reivaxy/iotinator/resources/4_modules.jpg

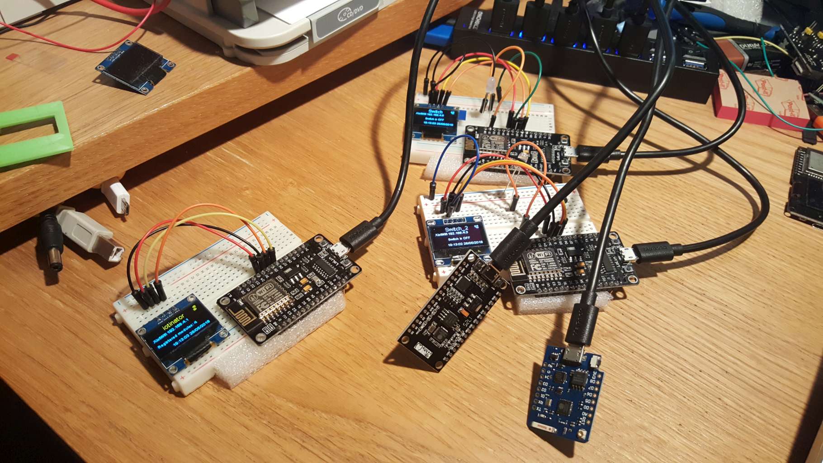
resources/4_modules.jpg
