reivaxy/iotinator/resources/boards.jpg

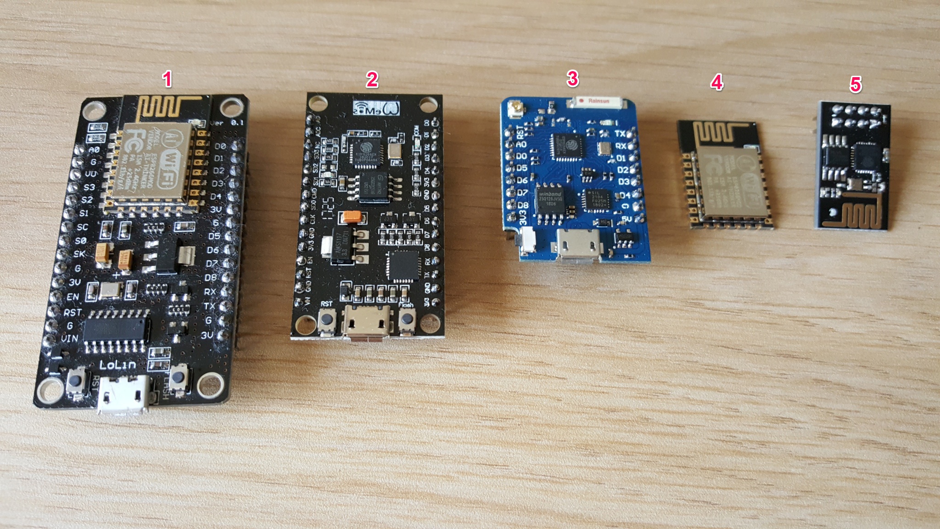
resources/boards.jpg
