reivaxy/iotinator/resources/customESP01.jpg

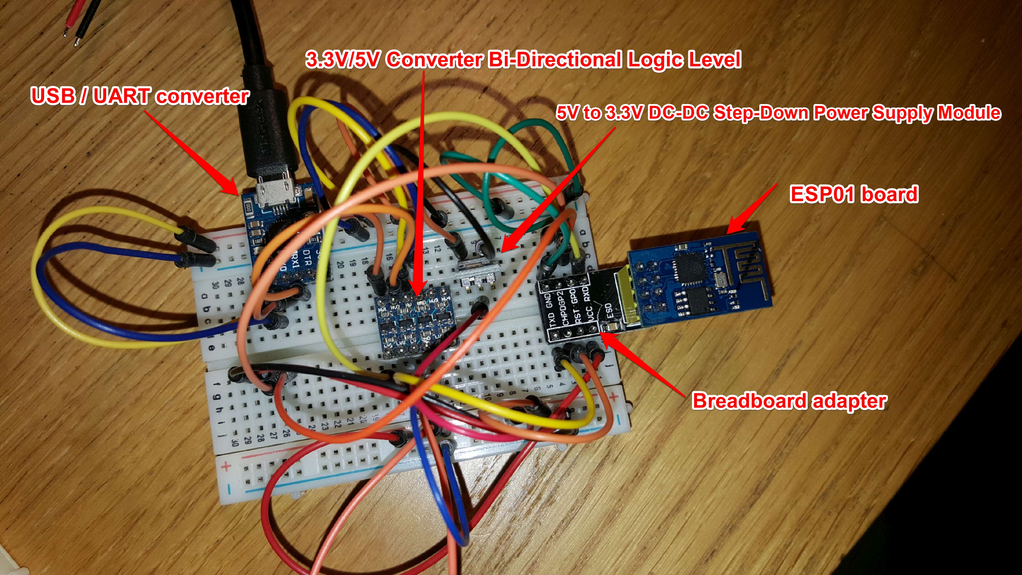
resources/customESP01.jpg
