reivaxy/iotinator/resources/esp01.jpg

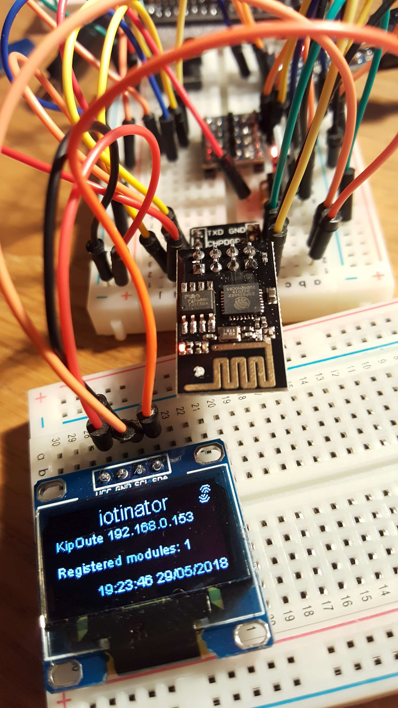
resources/esp01.jpg
