reivaxy/iotinator/resources/esp32.jpg

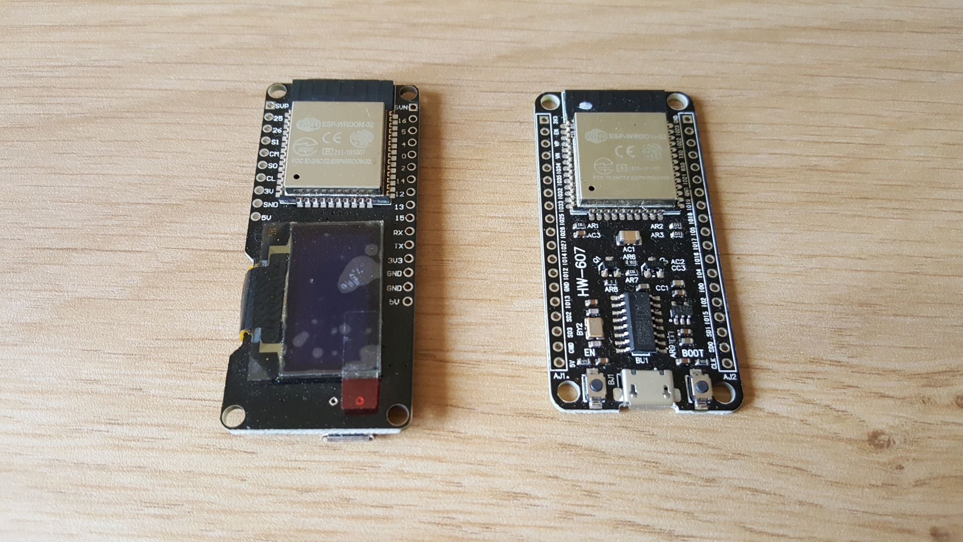
resources/esp32.jpg
