reivaxy/iotinator/resources/glyphEditor.png

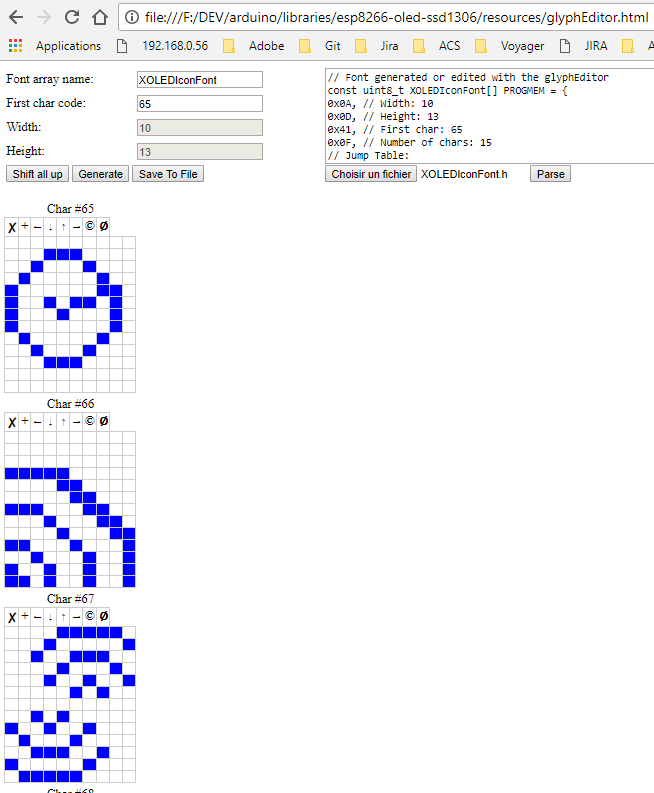
resources/glyphEditor.png
