reivaxy/iotinator/resources/heap.png

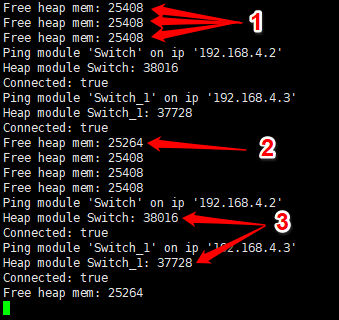
resources/heap.png
