reivaxy/iotinator/resources/iotinator_init_done.jpg

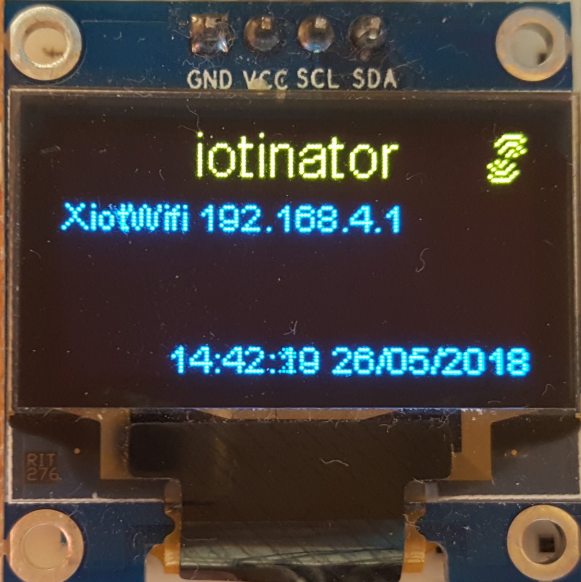
resources/iotinator_init_done.jpg
