reivaxy/iotinator/resources/iotinator_registration.jpg

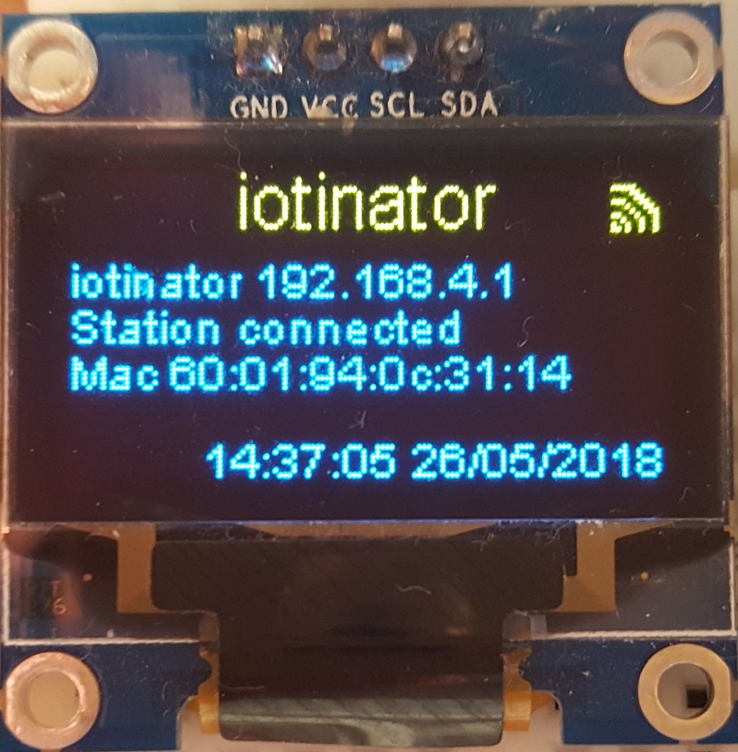
resources/iotinator_registration.jpg
