reivaxy/iotinator/resources/iotinator_waiting.jpg

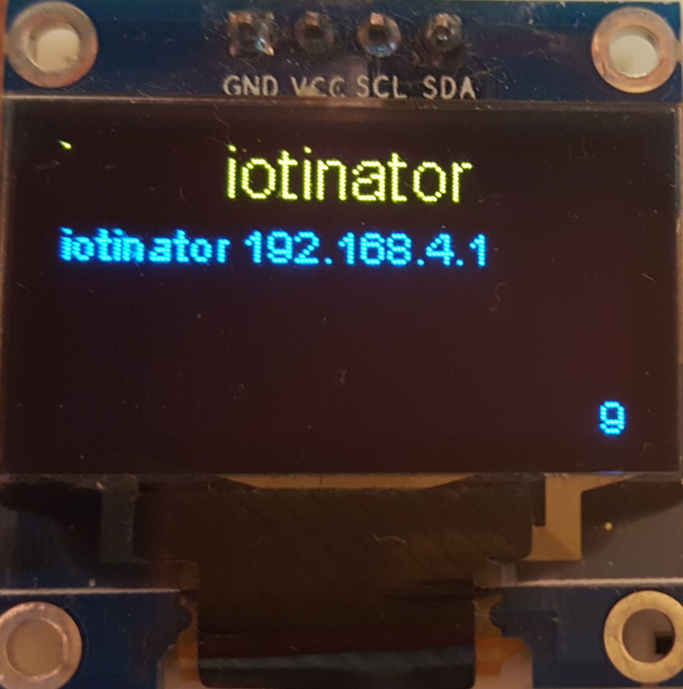
resources/iotinator_waiting.jpg
