reivaxy/iotinator/resources/OTA/OTA_loading.jpg

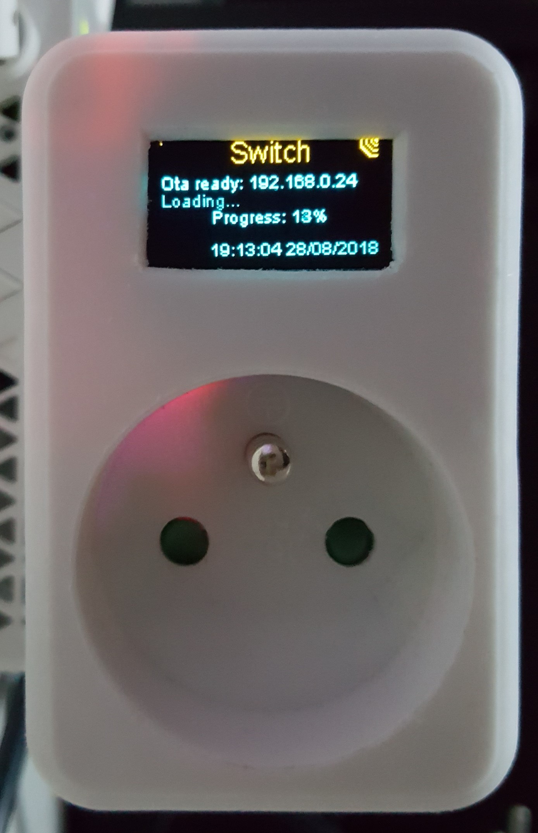
resources/OTA/OTA_loading.jpg
