reivaxy/iotinator/resources/OTA/OTA_ready.jpg

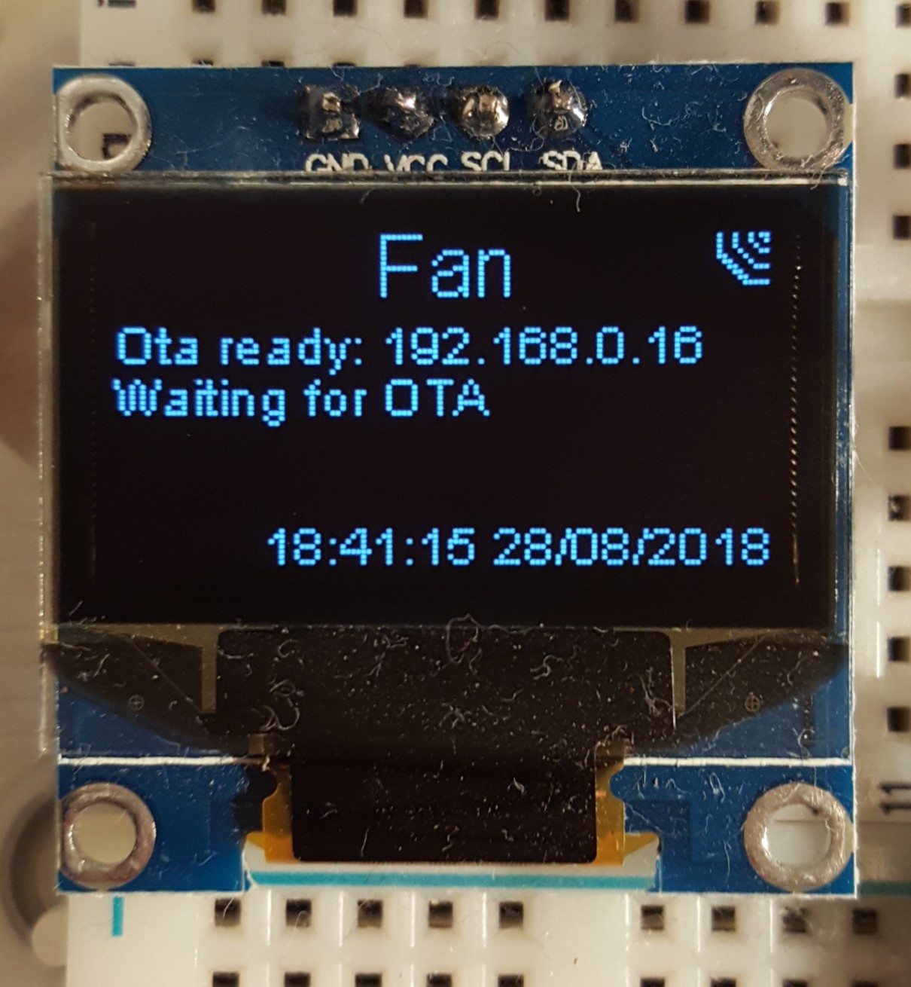
resources/OTA/OTA_ready.jpg
