reivaxy/iotinator/resources/prototype/backOpen.jpg

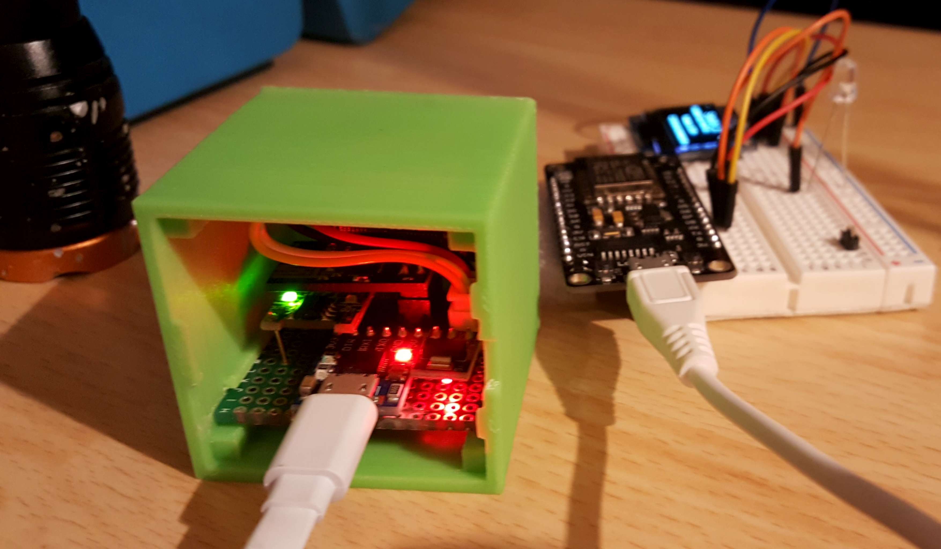
resources/prototype/backOpen.jpg
