reivaxy/iotinator/resources/prototype/backView.jpg

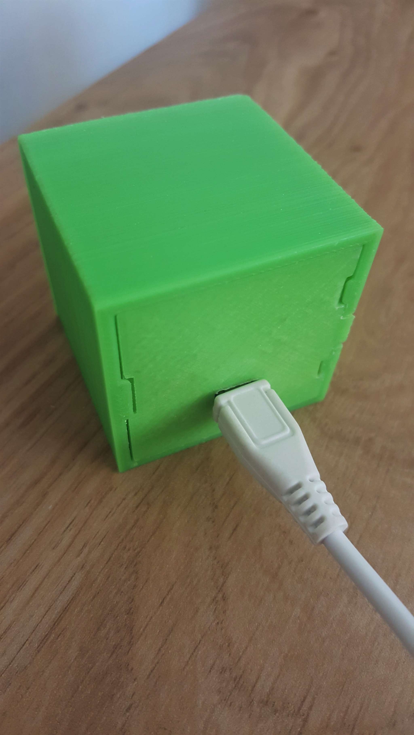
resources/prototype/backView.jpg
