reivaxy/iotinator/resources/prototype/case.jpg

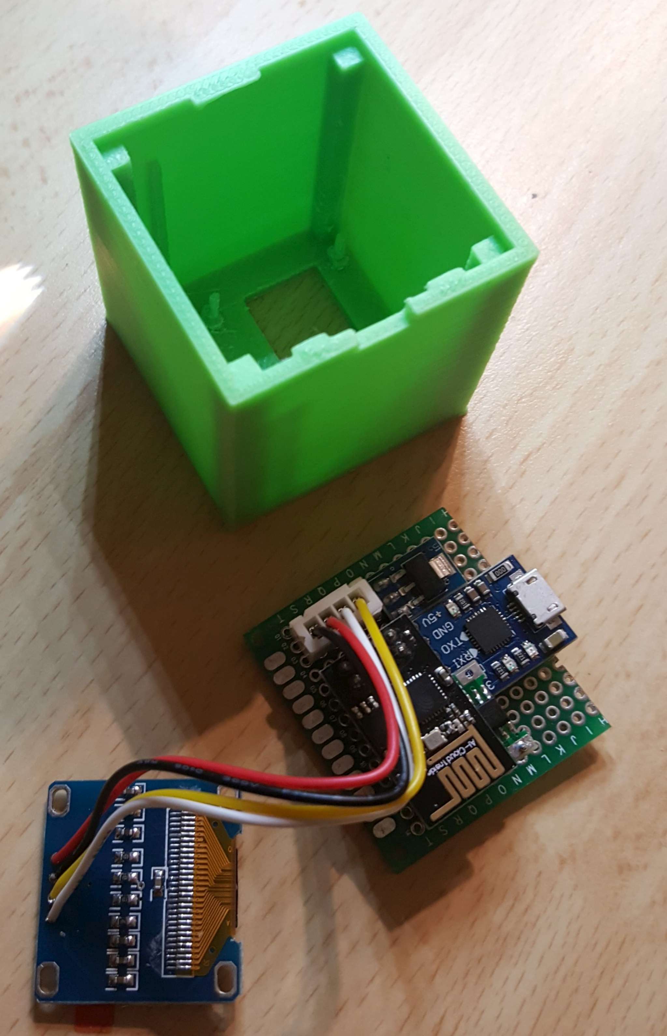
resources/prototype/case.jpg
