reivaxy/iotinator/resources/prototype/inPlace.jpg

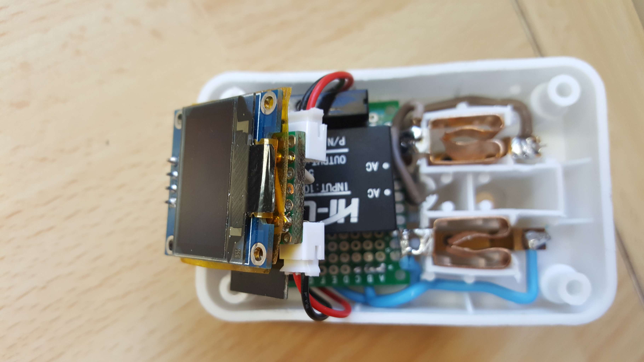
resources/prototype/inPlace.jpg
