reivaxy/iotinator/resources/prototype/mounted.jpg

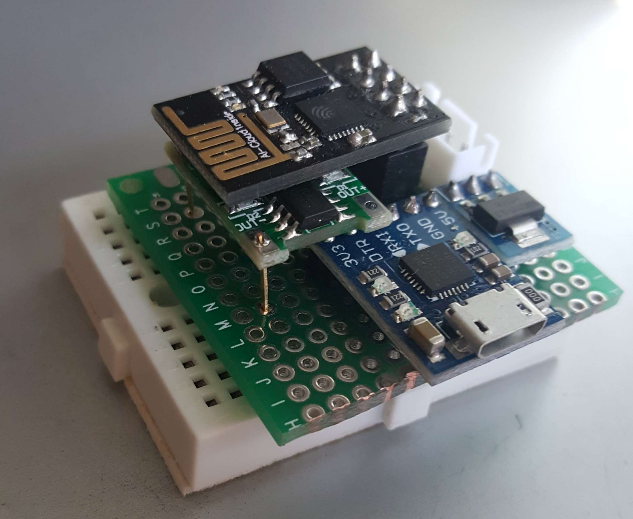
resources/prototype/mounted.jpg
