reivaxy/iotinator/resources/prototype/positioning.jpg

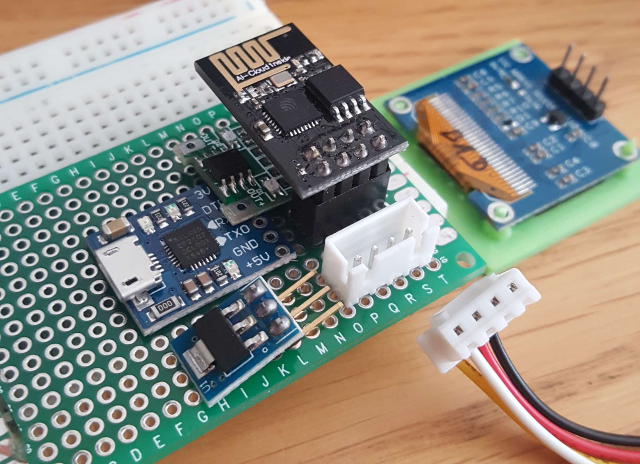
resources/prototype/positioning.jpg
