reivaxy/iotinator/resources/prototype/powerDown.jpg

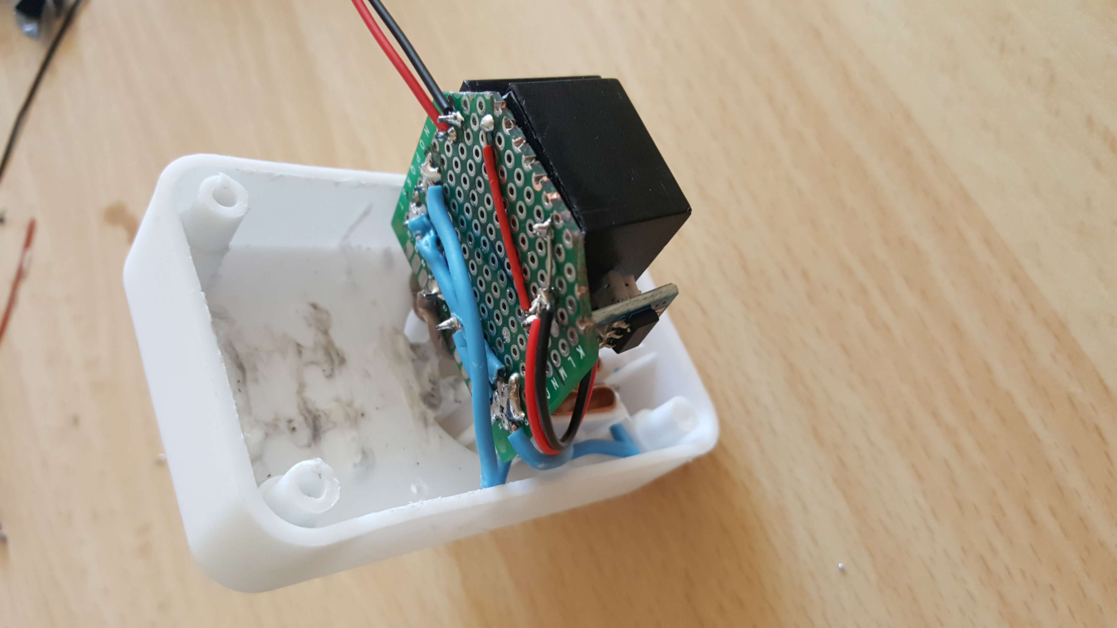
resources/prototype/powerDown.jpg
