reivaxy/iotinator/resources/prototype/powerSocketNew.jpg

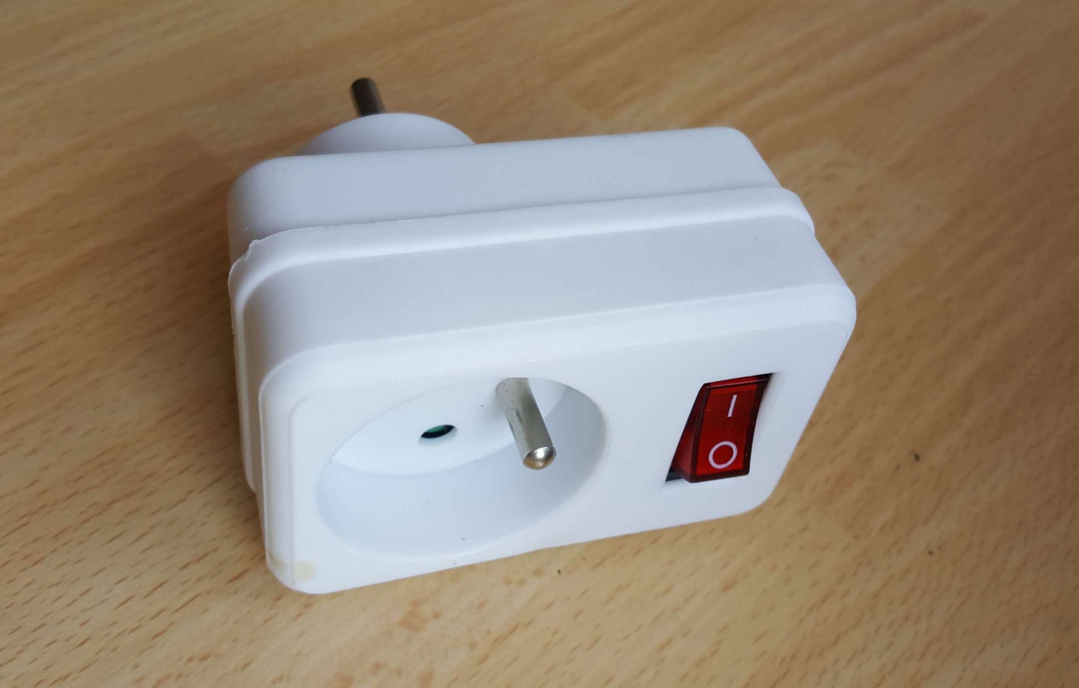
resources/prototype/powerSocketNew.jpg
