reivaxy/iotinator/resources/prototype/powerSocketOpen.jpg

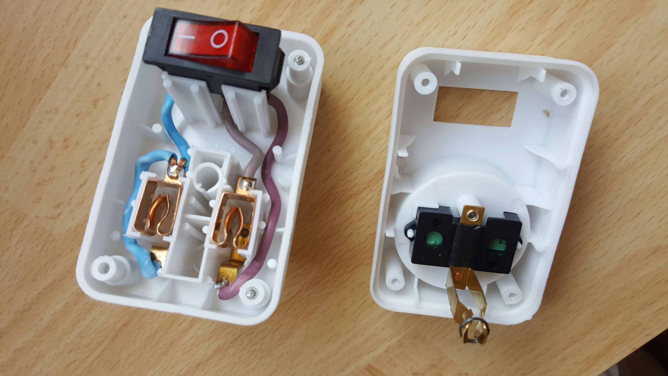
resources/prototype/powerSocketOpen.jpg
