reivaxy/iotinator/resources/prototype/ready.jpg

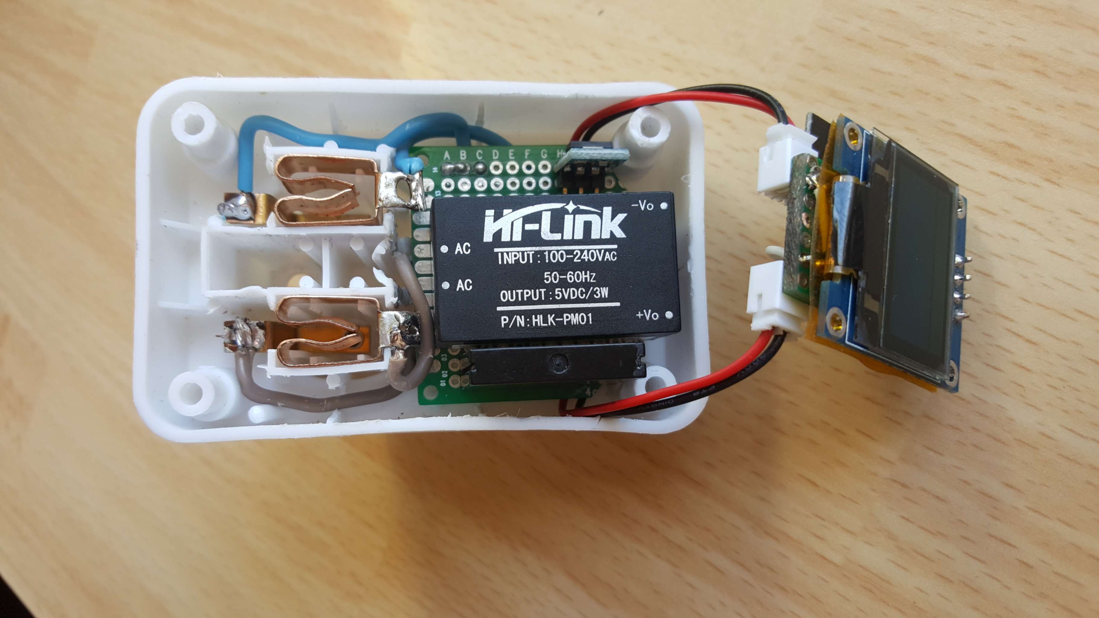
resources/prototype/ready.jpg
