reivaxy/iotinator/resources/prototype/sandwitch.jpg

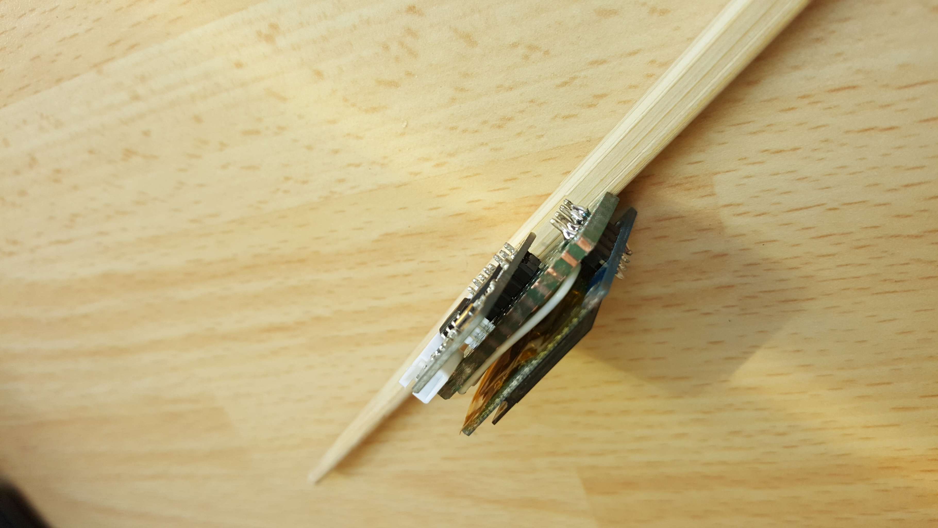
resources/prototype/sandwitch.jpg
