reivaxy/iotinator/resources/prototype/withScreen.jpg

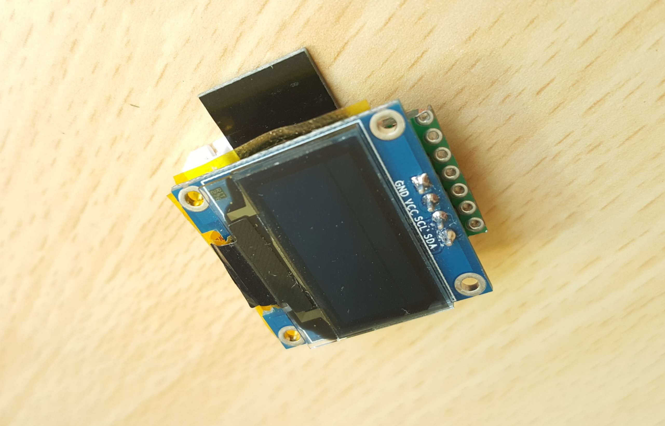
resources/prototype/withScreen.jpg
