reivaxy/iotinator/resources/switch_init1.jpg

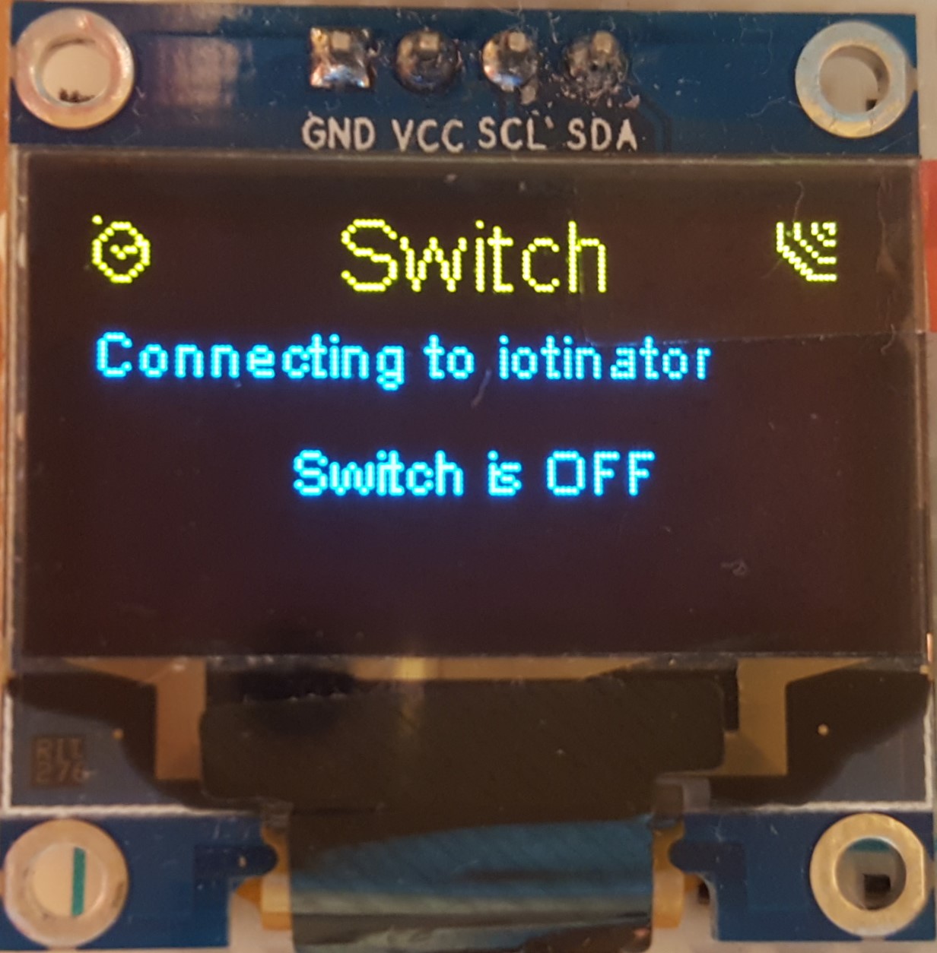
resources/switch_init1.jpg
