reivaxy/iotinator/resources/switch_init2.jpg

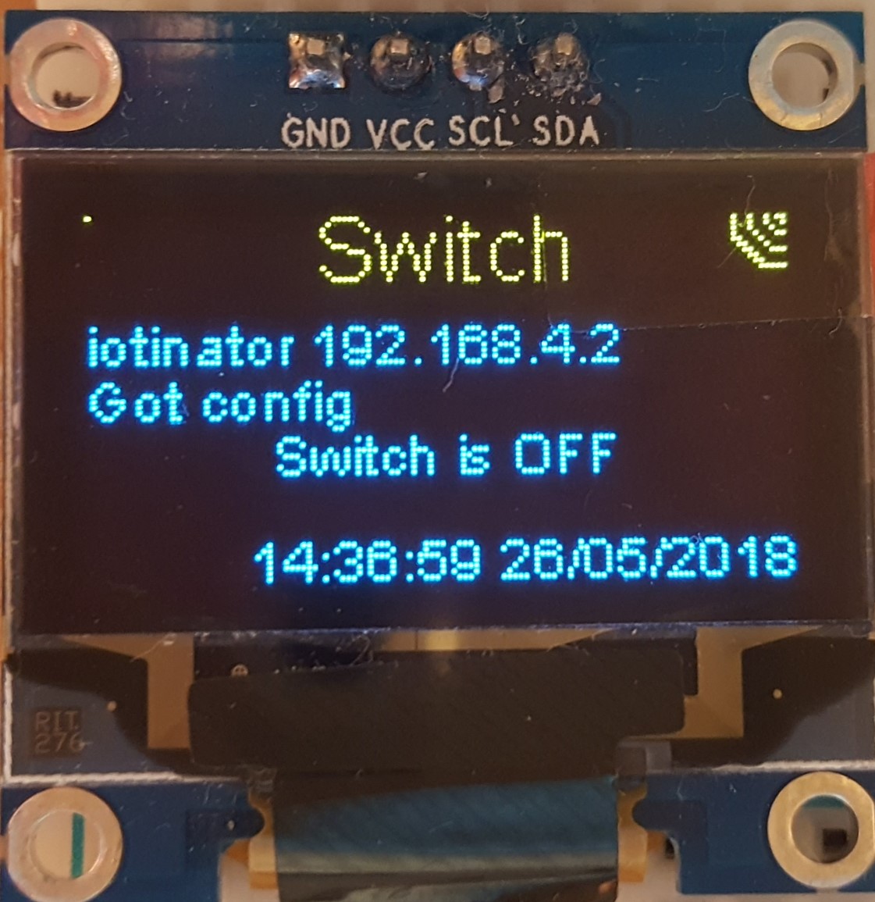
resources/switch_init2.jpg
