reivaxy/iotinator/resources/switch_on.jpg

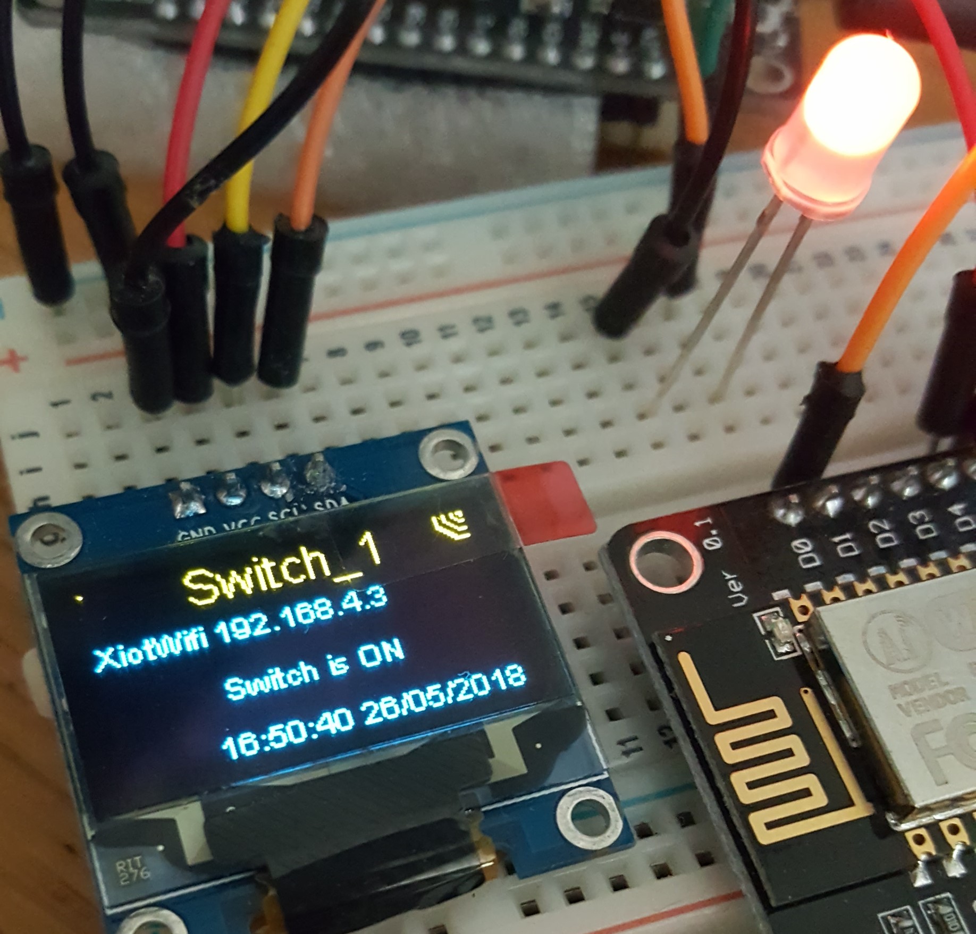
resources/switch_on.jpg
