reivaxy/iotinator/resources/usbESP01.jpg

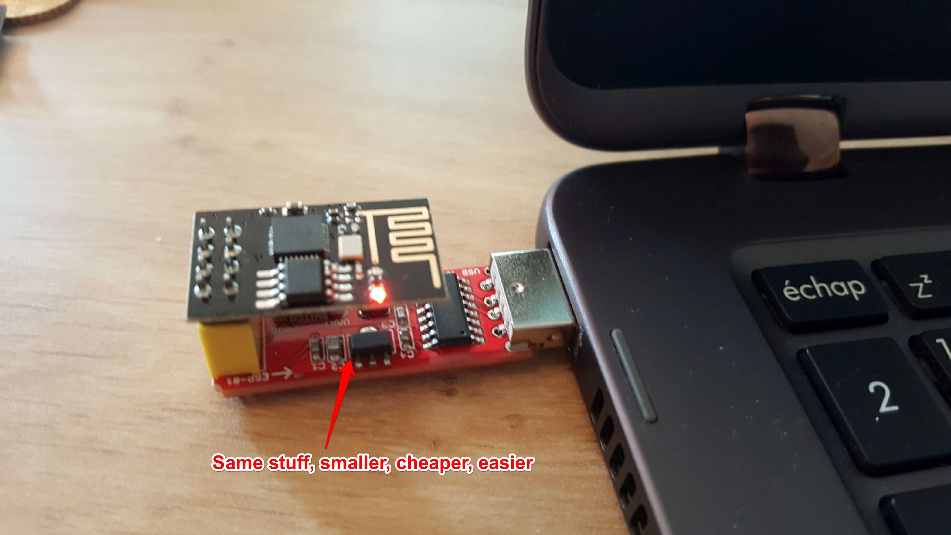
resources/usbESP01.jpg
