reivaxy/iotinator/resources/vcc_gnd.jpg

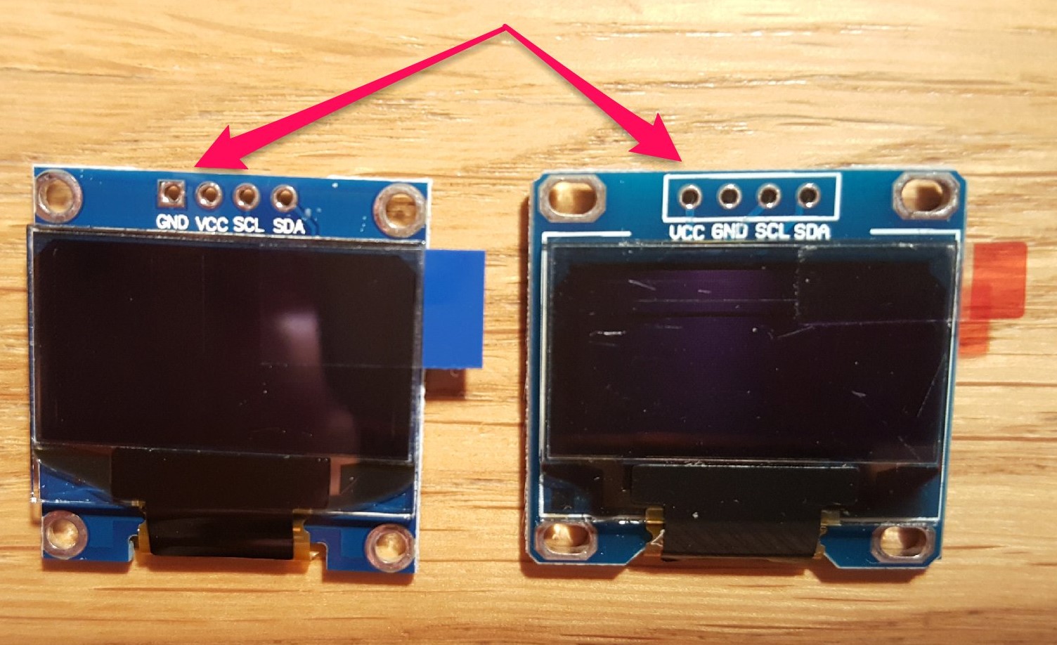
resources/vcc_gnd.jpg
