reivaxy/iotinator/resources/webApp_init.png

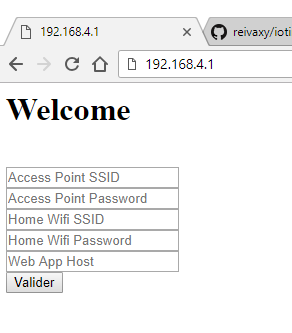
resources/webApp_init.png
