reivaxy/iotinator/resources/prototype/switchComponents.jpg

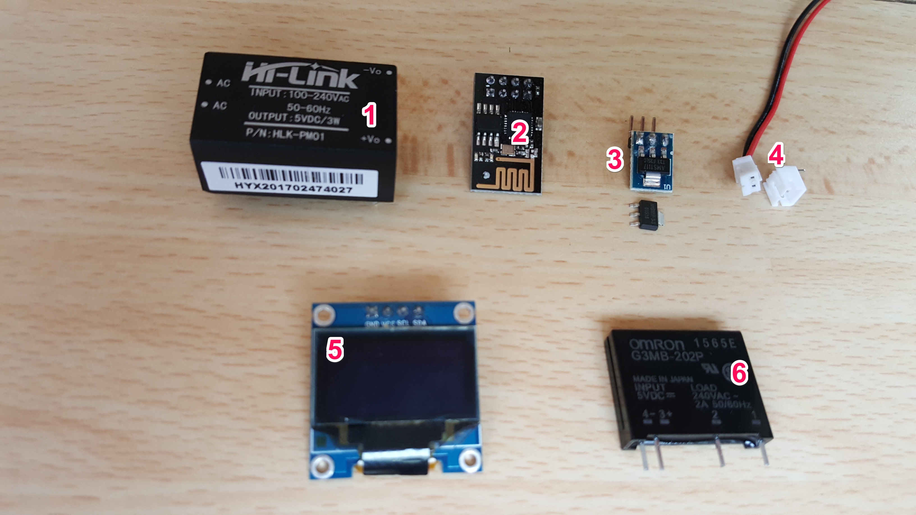
resources/prototype/switchComponents.jpg
