reivaxy/iotinator/resources/crappy_print.jpg

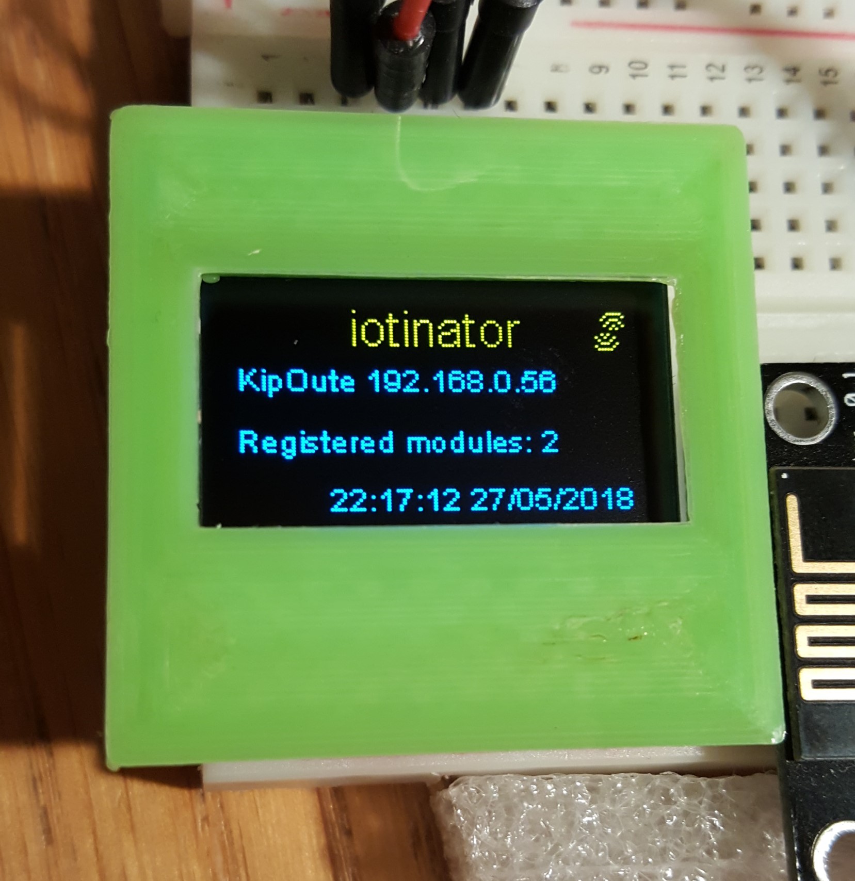
resources/crappy_print.jpg
