reivaxy/iotinator/resources/printed_panel.jpg

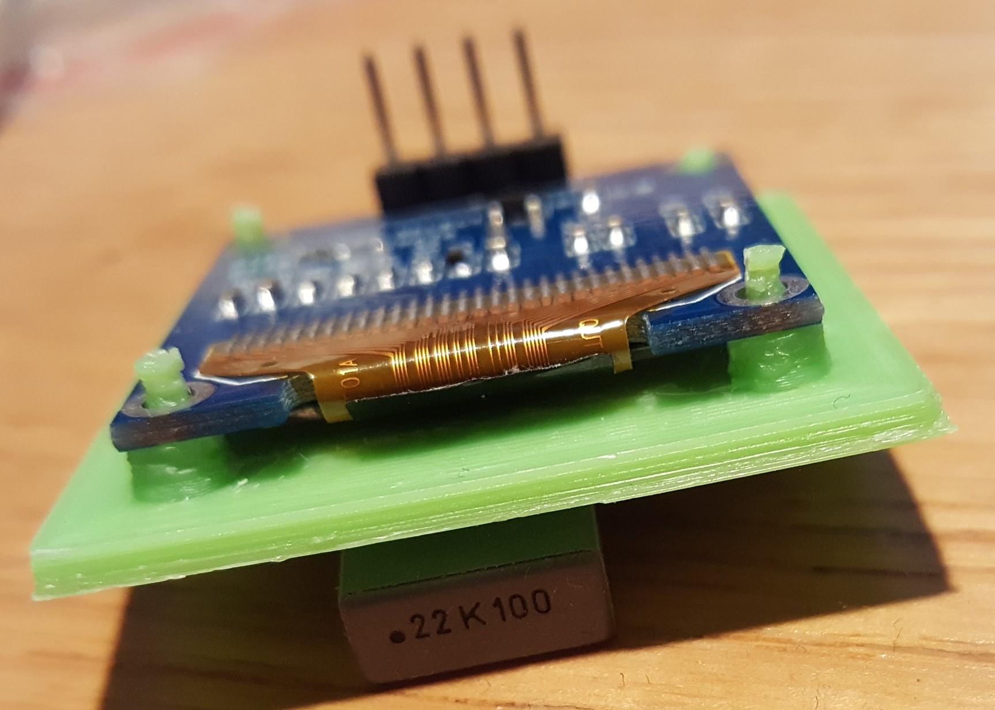
resources/printed_panel.jpg
