reivaxy/iotinator/resources/prototype/esp01Wiring.jpg

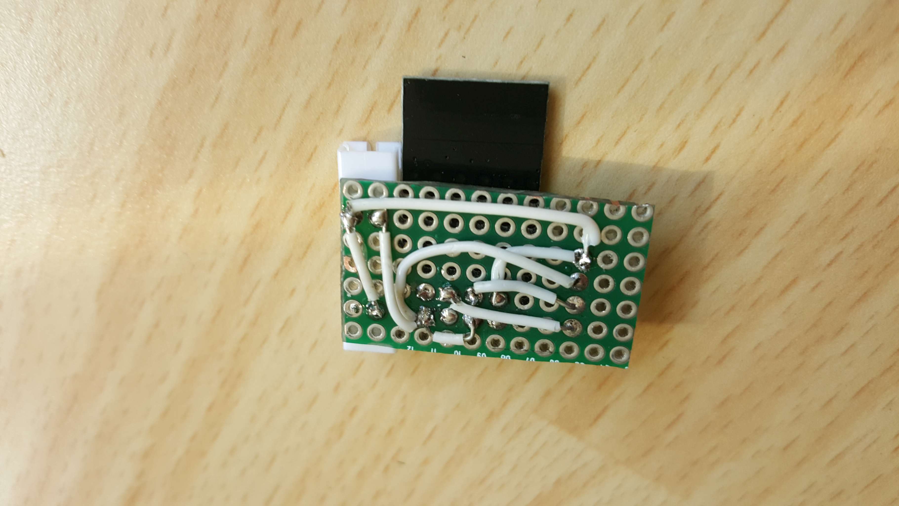
resources/prototype/esp01Wiring.jpg
