reivaxy/iotinator/resources/prototype/test.jpg

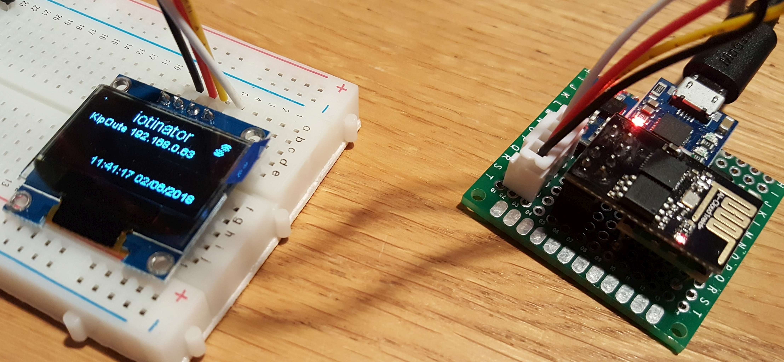
resources/prototype/test.jpg
