reivaxy/iotinator/resources/prototype/testingDCPower.jpg

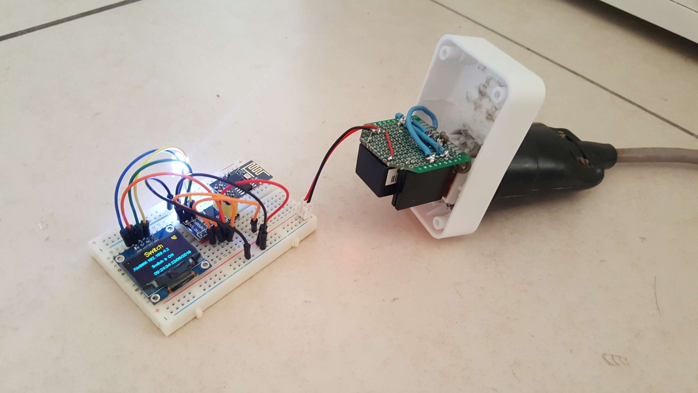
resources/prototype/testingDCPower.jpg
