reivaxy/iotinator/resources/webApp_debug.png

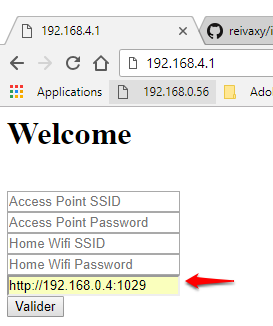
resources/webApp_debug.png
