reivaxy/iotinator/iotinator/src/Agent.cpp

/**
 *  Class handling Agent module registered in iotinator master
 *  Xavier Grosjean 2018
 *  Creative Commons Attribution-NonCommercial-ShareAlike 4.0 International Public License
 */

#include "Agent.h"

/*********************************************************************
 * Class to handle one agent module in master
 *
 *********************************************************************/
Agent::Agent(const char* name, const char* mac, XIOTModule* module) {
  XUtils::safeStringCopy(_name, name, NAME_MAX_LENGTH);
  XUtils::safeStringCopy(_mac, mac, NAME_MAX_LENGTH);
  _module = module;
  *_globalStatus = 0;
}

Agent::~Agent() {
  free(_custom);
}

const char* Agent::getName() {
  Debug("Agent::getName\n");
  return _name;
}
void Agent::setName(const char* name) {
  XUtils::safeStringCopy(_name, name, NAME_MAX_LENGTH);
}

const char* Agent::getIP() {
  Debug("Agent::getIP\n");
  return _ip;
}

const char* Agent::getMAC() {
  Debug("Agent::getMAC\n");
  return _mac;
}

void Agent::setIP(const char* ip) {
  XUtils::safeStringCopy(_ip, ip, DOUBLE_IP_MAX_LENGTH);
}

void Agent::setUiClassName(const char* uiClassName) {
  XUtils::safeStringCopy(_uiClassName, uiClassName, UI_CLASS_NAME_MAX_LENGTH);
}
const char* Agent::getUiClassName() {
  return _uiClassName;
}

int8_t Agent::getConnected() {
  return _connected;
}

void Agent::setToRename(bool flag) {
  _toRename = flag;
}

bool Agent::getToRename() {
  return _toRename;
}

void Agent::setHeap(uint32_t heap) {
  _heap = heap;
}

uint32_t Agent::getHeap() {
  return _heap;
}

bool Agent::getCanSleep() {
  return _canSleep;
}

void Agent::setCanSleep(bool canSleep) {
  _canSleep = canSleep;
}

int Agent::getPingPeriod() {
  return _pingPeriod;
}

void Agent::setPingPeriod(int pingPeriod) {
  // If value too small, keep default (legacy: when absent, value is 0)
  if(pingPeriod >= MIN_PING_PERIOD ) {
    _pingPeriod = pingPeriod;
  } else {
    _pingPeriod = 0;
  }
}
time_t Agent::getLastPing() {
  return _lastPing;
}

void Agent::setLastPing(time_t timestamp) {
  _lastPing = timestamp;
}

void Agent::setCustom(const char *custom) {
  Debug("Agent::setCustom\n");
  free(_custom); // This field is manually allocated, so it must be freed.
  _custom = NULL;

  if(custom == NULL) {
    _custom = NULL;
    return;
  }
  int size = strlen(custom);
  if(size > MAX_CUSTOM_DATA_SIZE) {
    Serial.println(CUSTOM_DATA_TOO_BIG_VALUE);
    size = strlen(CUSTOM_DATA_TOO_BIG_VALUE) ;
    _custom = (char *)malloc(size + 1);   // Will need to be freed, when we unregister agent, or overwrite one...
    XUtils::safeStringCopy(_custom, CUSTOM_DATA_TOO_BIG_VALUE, size);
  } else {
    _custom = (char *)malloc(size + 1);   // Will need to be freed, when we unregister agent, or overwrite one...
    XUtils::safeStringCopy(_custom, custom, size);
  }
}

const char* Agent::getCustom() {
  Debug("Agent::getCustom\n");
  if(_custom != NULL) {
    if(strcmp(_custom, CUSTOM_DATA_TOO_BIG_VALUE) == 0) {
      Serial.println(CUSTOM_DATA_TOO_BIG_VALUE);
      _module->getDisplay()->setLine(1, "Custom Data too big", TRANSIENT, NOT_BLINKING);
      _module->getDisplay()->setLine(2, getName(), TRANSIENT, NOT_BLINKING);
    }
  }
  return _custom;
}


const char* Agent::getGlobalStatus() {
  Debug("Agent::getGlobalStatus\n");
  if(strcmp(_globalStatus, GLOBAL_STATUS_TOO_BIG_VALUE) == 0) {
    Serial.println(GLOBAL_STATUS_TOO_BIG_VALUE);
    _module->getDisplay()->setLine(1, "Global Status too big", TRANSIENT, NOT_BLINKING);
    _module->getDisplay()->setLine(2, getName(), TRANSIENT, NOT_BLINKING);
  }

  return _globalStatus;
}


void Agent::setGlobalStatus(const char *globalStatus) {
  Debug("Agent::setGlobalStatus\n");

  if(globalStatus == NULL) {
    *_globalStatus = 0;
    return;
  }
  int size = strlen(globalStatus);
  if(size > MAX_GLOBAL_STATUS_SIZE) {
    Serial.println(GLOBAL_STATUS_TOO_BIG_VALUE);
    strlcpy(_globalStatus, GLOBAL_STATUS_TOO_BIG_VALUE, MAX_GLOBAL_STATUS_SIZE+1);
  } else {
    strlcpy(_globalStatus, globalStatus, MAX_GLOBAL_STATUS_SIZE+1);
  }
}

void Agent::renameTo(const char* newName) {
  Debug("Agent::renameTo %s\n", getIP());  // ip is easier for debug since displayed on agents
  int httpCode;
  char renameMsg[101];
  const int bufferSize = JSON_OBJECT_SIZE(1);
  StaticJsonBuffer<bufferSize> jsonBuffer;
  JsonObject& root = jsonBuffer.createObject();
  root[XIOTModuleJsonTag::name] = newName ;
  root.printTo(renameMsg, 100);
  Serial.printf("Renaming payload: %s\n", renameMsg);   
  _module->APIPost(getIP(), "/api/rename", renameMsg, &httpCode);
  if(httpCode != 200) {
    _module->getDisplay()->setLine(1, "Renaming failed", TRANSIENT, NOT_BLINKING);
  } else {
    sprintf(renameMsg, "Renamed %s", newName);
    _module->getDisplay()->setLine(1, renameMsg, TRANSIENT, NOT_BLINKING);
    _toRename = false;
    setName(newName);
  }  
}

// Returns 0 if module was not pinged due to ping period or canSleep flag
// Returns 1 if ping was successfull
// Returns -1 if ping failed
int8_t Agent::ping() {
  Debug("Agent::ping\n");
  int httpCode;

  time_t now = millis();
  bool elapsed = false;
  if(_pingPeriod > 0) {
    elapsed = (now >= (_lastPing + (_pingPeriod*1000)));
  } else {
    _connected = 0;  // do not ping : can't tell if connected or not.
  }
  if(_canSleep || !elapsed) {
    if(_canSleep) {
      _connected = 0;
    }
    Serial.printf("Not pinging module '%s' on ip '%s': canSleep: %d, pingPeriod: %d\n", _name, _ip, _canSleep, _pingPeriod);
    return 0;    
  }
  _lastPing = now; 
  
  Serial.printf("Ping module '%s' on ip '%s' pingPeriod %d\n", _name, _ip, _pingPeriod);
  
  int resultSize = 100 + MAX_CUSTOM_DATA_SIZE; 
  char resultPayload[resultSize];
  _module->APIGet(_ip, "/api/ping", &httpCode, resultPayload, resultSize);

  if(httpCode == 200) {
    _connected = 1;
    const int bufferSize = JSON_OBJECT_SIZE(2);  // At most 2 fields in one object
    StaticJsonBuffer<bufferSize> jsonBuffer;
    JsonObject& root = jsonBuffer.parseObject(resultPayload);
    int heap = root[XIOTModuleJsonTag::heap];
    Serial.printf("Heap module %s: %d\n", getName(), heap);
    setHeap(heap);
    Debug("Custom: %s\n", (const char *)root[XIOTModuleJsonTag::custom]);
    setCustom(root[XIOTModuleJsonTag::custom]);  
  } else {
    _connected = -1;
    char message[100];
    sprintf(message, "Ping failed: %s", _name);
    _module->getDisplay()->setLine(1, message, TRANSIENT, NOT_BLINKING); 
  }
  
  Serial.printf("Connected: %s\n", _connected == 1?"true":"false");
  return _connected;
}

bool Agent::reset() {
  Debug("Agent::reset\n");
  int httpCode;
  _module->APIGet(getIP(), "/api/moduleReset", &httpCode);  
  return (httpCode == 200);
}
