reivaxy/iotinator/iotinator/include/messages_en.h

/**
 *  master module english messages 
 *  Xavier Grosjean 2017
 *  Creative Commons Attribution-NonCommercial-ShareAlike 4.0 International Public License
 */
 
#pragma once

#define MSG_INIT_WELCOME "Welcome"
#define MSG_INIT_ADMIN_PHONE_NUMBER "Admin Phone Number"
#define MSG_INIT_AP_SSID "Access Point SSID"
#define MSG_INIT_AP_PWD "Access Point Password"
#define MSG_INIT_HOME_SSID "Home Wifi SSID"
#define MSG_INIT_HOME_PWD "Home Wifi Password"
#define MSG_INIT_NTP_HOST "Time server NTP Host"
#define MSG_INIT_WEBSITE "Web site URL"
#define MSG_INIT_API_KEY "Api Key from Web site registration"
#define MSG_INIT_SIM_PIN "SIM PIN"

#define MSG_INIT_REQUEST "Please initialize"
#define MSG_INIT_DONE "Init done"
#define MSG_INIT_ALREADY_DONE "Init already done"

#define MSG_WIFI_OPENING_AP "Opening Access Point "
#define MSG_WIFI_CONNECTING_HOME "Connecting to Home WiFi "
#define MSG_WIFI_CONNECTED_HOME "Connected to Home WiFi "
#define MSG_WIFI_HOME_TIMEOUT "Home WiFi Connection time out"
#define MSG_WIFI_STATION_CONNECTED "Station connected"
#define MSG_WIFI_STATION_DISCONNECTED "Station disconnected"


#define MSG_ERR_ALREADY_INITIALIZED "Forbidden page, already initialized"
#define MSG_ERR_BAD_REQUEST "Bad Request"
#define MSG_ERR_PASSWORD_LENGTH "Password must be at least 8 characters"
#define MSG_ERR_ADMIN_LENGTH "Admin phone number must be at least 10 characters"
#define MSG_ERR_PIN_LENGTH "PIN SIM must be 4 characters"
