reivaxy/iotinator/iotinator/include/messages.h

/**
 *  iotinator localization file.
 *  Replace the included file with the one translated to your language choice. 
 *  Xavier Grosjean 2017
 *  Creative Commons Attribution-NonCommercial-ShareAlike 4.0 International Public License
 */
 
#pragma once

#include "messages_en.h"
